leonrinkel/sam-fd/software/baremetal/inc/port.h

/* SPDX-License-Identifier: MIT */
/**
 * \file      inc/port.h
 * \brief     Definitions regarding PORT registers structure
 * \copyright Copyright (c) 2023 Leon Rinkel
 */

#ifndef SAMFD_PORT_H
#define SAMFD_PORT_H

#include <stdint.h>

/** \brief PORT registers base address */
#define PORT_ADDR 0x41000000u

/** \name PORT DIR register */
/**@{*/

/** \brief PORT DIR register structure */
typedef union
{
	/** \brief Unsigned access */
	uint32_t U;
	/** \brief Bitfield access */
	struct
	{
		/** \brief Port data direction for pin 0 */
		uint32_t DIR0:1;
		/** \brief Port data direction for pin 1 */
		uint32_t DIR1:1;
		/** \brief Port data direction for pin 2 */
		uint32_t DIR2:1;
		/** \brief Port data direction for pin 3 */
		uint32_t DIR3:1;
		/** \brief Port data direction for pin 4 */
		uint32_t DIR4:1;
		/** \brief Port data direction for pin 5 */
		uint32_t DIR5:1;
		/** \brief Port data direction for pin 6 */
		uint32_t DIR6:1;
		/** \brief Port data direction for pin 7 */
		uint32_t DIR7:1;
		/** \brief Port data direction for pin 8 */
		uint32_t DIR8:1;
		/** \brief Port data direction for pin 9 */
		uint32_t DIR9:1;
		/** \brief Port data direction for pin 10 */
		uint32_t DIR10:1;
		/** \brief Port data direction for pin 11 */
		uint32_t DIR11:1;
		/** \brief Port data direction for pin 12 */
		uint32_t DIR12:1;
		/** \brief Port data direction for pin 13 */
		uint32_t DIR13:1;
		/** \brief Port data direction for pin 14 */
		uint32_t DIR14:1;
		/** \brief Port data direction for pin 15 */
		uint32_t DIR15:1;
		/** \brief Port data direction for pin 16 */
		uint32_t DIR16:1;
		/** \brief Port data direction for pin 17 */
		uint32_t DIR17:1;
		/** \brief Port data direction for pin 18 */
		uint32_t DIR18:1;
		/** \brief Port data direction for pin 19 */
		uint32_t DIR19:1;
		/** \brief Port data direction for pin 20 */
		uint32_t DIR20:1;
		/** \brief Port data direction for pin 21 */
		uint32_t DIR21:1;
		/** \brief Port data direction for pin 22 */
		uint32_t DIR22:1;
		/** \brief Port data direction for pin 23 */
		uint32_t DIR23:1;
		/** \brief Port data direction for pin 24 */
		uint32_t DIR24:1;
		/** \brief Port data direction for pin 25 */
		uint32_t DIR25:1;
		/** \brief Port data direction for pin 26 */
		uint32_t DIR26:1;
		/** \brief Port data direction for pin 27 */
		uint32_t DIR27:1;
		/** \brief Port data direction for pin 28 */
		uint32_t DIR28:1;
		/** \brief Port data direction for pin 29 */
		uint32_t DIR29:1;
		/** \brief Port data direction for pin 30 */
		uint32_t DIR30:1;
		/** \brief Port data direction for pin 31 */
		uint32_t DIR31:1;
	} B;
} port_dir_t;

/** \brief PORT DIR register address offset */
#define PORT_DIR_OFF 0x00u

/** \brief PORT DIR register address */
#define PORT_DIR_ADDR (PORT_ADDR + PORT_DIR_OFF)

/** \brief PORT DIR register */
#define PORT_DIR (*((volatile port_dir_t*) PORT_DIR_ADDR))

/** \brief PORT DIR.DIR0 bit offset */
#define PORT_DIR_DIR0_OFF 0u
/** \brief PORT DIR.DIR0 bit mask */
#define PORT_DIR_DIR0_MSK (0x1u << PORT_DIR_DIR0_OFF)

/** \brief PORT DIR.DIR1 bit offset */
#define PORT_DIR_DIR1_OFF 1u
/** \brief PORT DIR.DIR1 bit mask */
#define PORT_DIR_DIR1_MSK (0x1u << PORT_DIR_DIR1_OFF)

/** \brief PORT DIR.DIR2 bit offset */
#define PORT_DIR_DIR2_OFF 2u
/** \brief PORT DIR.DIR2 bit mask */
#define PORT_DIR_DIR2_MSK (0x1u << PORT_DIR_DIR2_OFF)

/** \brief PORT DIR.DIR3 bit offset */
#define PORT_DIR_DIR3_OFF 3u
/** \brief PORT DIR.DIR3 bit mask */
#define PORT_DIR_DIR3_MSK (0x1u << PORT_DIR_DIR3_OFF)

/** \brief PORT DIR.DIR4 bit offset */
#define PORT_DIR_DIR4_OFF 4u
/** \brief PORT DIR.DIR4 bit mask */
#define PORT_DIR_DIR4_MSK (0x1u << PORT_DIR_DIR4_OFF)

/** \brief PORT DIR.DIR5 bit offset */
#define PORT_DIR_DIR5_OFF 5u
/** \brief PORT DIR.DIR5 bit mask */
#define PORT_DIR_DIR5_MSK (0x1u << PORT_DIR_DIR5_OFF)

/** \brief PORT DIR.DIR6 bit offset */
#define PORT_DIR_DIR6_OFF 6u
/** \brief PORT DIR.DIR6 bit mask */
#define PORT_DIR_DIR6_MSK (0x1u << PORT_DIR_DIR6_OFF)

/** \brief PORT DIR.DIR7 bit offset */
#define PORT_DIR_DIR7_OFF 7u
/** \brief PORT DIR.DIR7 bit mask */
#define PORT_DIR_DIR7_MSK (0x1u << PORT_DIR_DIR7_OFF)

/** \brief PORT DIR.DIR8 bit offset */
#define PORT_DIR_DIR8_OFF 8u
/** \brief PORT DIR.DIR8 bit mask */
#define PORT_DIR_DIR8_MSK (0x1u << PORT_DIR_DIR8_OFF)

/** \brief PORT DIR.DIR9 bit offset */
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
#define PORT_OUT_OUT18_OFF 18u
/** \brief PORT OUT.OUT18 bit mask */
#define PORT_OUT_OUT18_MSK (0x1u << PORT_OUT_OUT18_OFF)

/** \brief PORT OUT.OUT19 bit offset */
#define PORT_OUT_OUT19_OFF 19u
/** \brief PORT OUT.OUT19 bit mask */
#define PORT_OUT_OUT19_MSK (0x1u << PORT_OUT_OUT19_OFF)

/** \brief PORT OUT.OUT20 bit offset */
#define PORT_OUT_OUT20_OFF 20u
/** \brief PORT OUT.OUT20 bit mask */
#define PORT_OUT_OUT20_MSK (0x1u << PORT_OUT_OUT20_OFF)

/** \brief PORT OUT.OUT21 bit offset */
#define PORT_OUT_OUT21_OFF 21u
/** \brief PORT OUT.OUT21 bit mask */
#define PORT_OUT_OUT21_MSK (0x1u << PORT_OUT_OUT21_OFF)

/** \brief PORT OUT.OUT22 bit offset */
#define PORT_OUT_OUT22_OFF 22u
/** \brief PORT OUT.OUT22 bit mask */
#define PORT_OUT_OUT22_MSK (0x1u << PORT_OUT_OUT22_OFF)

/** \brief PORT OUT.OUT23 bit offset */
#define PORT_OUT_OUT23_OFF 23u
/** \brief PORT OUT.OUT23 bit mask */
#define PORT_OUT_OUT23_MSK (0x1u << PORT_OUT_OUT23_OFF)

/** \brief PORT OUT.OUT24 bit offset */
#define PORT_OUT_OUT24_OFF 24u
/** \brief PORT OUT.OUT24 bit mask */
#define PORT_OUT_OUT24_MSK (0x1u << PORT_OUT_OUT24_OFF)

/** \brief PORT OUT.OUT25 bit offset */
#define PORT_OUT_OUT25_OFF 25u
/** \brief PORT OUT.OUT25 bit mask */
#define PORT_OUT_OUT25_MSK (0x1u << PORT_OUT_OUT25_OFF)

/** \brief PORT OUT.OUT26 bit offset */
#define PORT_OUT_OUT26_OFF 26u
/** \brief PORT OUT.OUT26 bit mask */
#define PORT_OUT_OUT26_MSK (0x1u << PORT_OUT_OUT26_OFF)

/** \brief PORT OUT.OUT27 bit offset */
#define PORT_OUT_OUT27_OFF 27u
/** \brief PORT OUT.OUT27 bit mask */
#define PORT_OUT_OUT27_MSK (0x1u << PORT_OUT_OUT27_OFF)

/** \brief PORT OUT.OUT28 bit offset */
#define PORT_OUT_OUT28_OFF 28u
/** \brief PORT OUT.OUT28 bit mask */
#define PORT_OUT_OUT28_MSK (0x1u << PORT_OUT_OUT28_OFF)

/** \brief PORT OUT.OUT29 bit offset */
#define PORT_OUT_OUT29_OFF 29u
/** \brief PORT OUT.OUT29 bit mask */
#define PORT_OUT_OUT29_MSK (0x1u << PORT_OUT_OUT29_OFF)

/** \brief PORT OUT.OUT30 bit offset */
#define PORT_OUT_OUT30_OFF 30u
/** \brief PORT OUT.OUT30 bit mask */
#define PORT_OUT_OUT30_MSK (0x1u << PORT_OUT_OUT30_OFF)

/** \brief PORT OUT.OUT31 bit offset */
#define PORT_OUT_OUT31_OFF 31u
/** \brief PORT OUT.OUT31 bit mask */
#define PORT_OUT_OUT31_MSK (0x1u << PORT_OUT_OUT31_OFF)

/**@}*/

/** \name PORT PINCFG register */
/**@{*/

/** \brief PORT PINCFG register structure */
typedef union
{
	/** \brief Unsigned access */
	uint8_t U;
	/** \brief Bitfield access */
	struct
	{
		/** \brief Peripheral multiplexer enable */
		uint8_t PMUXEN:1;
		/** \brief Input buffer enable */
		uint8_t INEN:1;
		/** \brief Pull enable */
		uint8_t PULLEN:1;
		/** \brief Reserved */
		uint8_t :3;
		/** \brief Output driver strength selection */
		uint8_t DRVSTR:1;
		/** \brief Reserved */
		uint8_t :1;
	} B;
} port_pincfg_t;

/** \brief PORT PINCFG0 register address offset */
#define PORT_PINCFG0_OFF 0x40u
/** \brief PORT PINCFG1 register address offset */
#define PORT_PINCFG1_OFF 0x41u
/** \brief PORT PINCFG2 register address offset */
#define PORT_PINCFG2_OFF 0x42u
/** \brief PORT PINCFG3 register address offset */
#define PORT_PINCFG3_OFF 0x43u
/** \brief PORT PINCFG4 register address offset */
#define PORT_PINCFG4_OFF 0x44u
/** \brief PORT PINCFG5 register address offset */
#define PORT_PINCFG5_OFF 0x45u
/** \brief PORT PINCFG6 register address offset */
#define PORT_PINCFG6_OFF 0x46u
/** \brief PORT PINCFG7 register address offset */
#define PORT_PINCFG7_OFF 0x47u
/** \brief PORT PINCFG8 register address offset */
#define PORT_PINCFG8_OFF 0x48u
/** \brief PORT PINCFG9 register address offset */
#define PORT_PINCFG9_OFF 0x49u
/** \brief PORT PINCFG10 register address offset */
#define PORT_PINCFG10_OFF 0x4Au
/** \brief PORT PINCFG11 register address offset */
#define PORT_PINCFG11_OFF 0x4Bu
/** \brief PORT PINCFG12 register address offset */
#define PORT_PINCFG12_OFF 0x4Cu
/** \brief PORT PINCFG13 register address offset */
#define PORT_PINCFG13_OFF 0x4Du
/** \brief PORT PINCFG14 register address offset */
#define PORT_PINCFG14_OFF 0x4Eu
/** \brief PORT PINCFG15 register address offset */
#define PORT_PINCFG15_OFF 0x4Fu
/** \brief PORT PINCFG16 register address offset */
#define PORT_PINCFG16_OFF 0x50u
/** \brief PORT PINCFG17 register address offset */
#define PORT_PINCFG17_OFF 0x51u
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
/** \brief PORT PINCFG22 register */
#define PORT_PINCFG22 (*((volatile port_pincfg_t*) PORT_PINCFG22_ADDR))
/** \brief PORT PINCFG23 register */
#define PORT_PINCFG23 (*((volatile port_pincfg_t*) PORT_PINCFG23_ADDR))
/** \brief PORT PINCFG24 register */
#define PORT_PINCFG24 (*((volatile port_pincfg_t*) PORT_PINCFG24_ADDR))
/** \brief PORT PINCFG25 register */
#define PORT_PINCFG25 (*((volatile port_pincfg_t*) PORT_PINCFG25_ADDR))
/** \brief PORT PINCFG26 register */
#define PORT_PINCFG26 (*((volatile port_pincfg_t*) PORT_PINCFG26_ADDR))
/** \brief PORT PINCFG27 register */
#define PORT_PINCFG27 (*((volatile port_pincfg_t*) PORT_PINCFG27_ADDR))
/** \brief PORT PINCFG28 register */
#define PORT_PINCFG28 (*((volatile port_pincfg_t*) PORT_PINCFG28_ADDR))
/** \brief PORT PINCFG29 register */
#define PORT_PINCFG29 (*((volatile port_pincfg_t*) PORT_PINCFG29_ADDR))
/** \brief PORT PINCFG30 register */
#define PORT_PINCFG30 (*((volatile port_pincfg_t*) PORT_PINCFG30_ADDR))
/** \brief PORT PINCFG31 register */
#define PORT_PINCFG31 (*((volatile port_pincfg_t*) PORT_PINCFG31_ADDR))

/** \brief PORT PINCFG.PMUXEN bit offset */
#define PORT_PINCFG_PMUXEN_OFF 0u
/** \brief PORT PINCFG.PMUXEN bit mask */
#define PORT_PINCFG_PMUXEN_MSK (0x1u << PORT_PINCFG_PMUXEN_OFF)

/** \brief PORT PINCFG.INEN bit offset */
#define PORT_PINCFG_INEN_OFF 1u
/** \brief PORT PINCFG.INEN bit mask */
#define PORT_PINCFG_INEN_MSK (0x1u << PORT_PINCFG_INEN_OFF)

/** \brief PORT PINCFG.PULLEN bit offset */
#define PORT_PINCFG_PULLEN_OFF 2u
/** \brief PORT PINCFG.PULLEN bit mask */
#define PORT_PINCFG_PULLEN_MSK (0x1u << PORT_PINCFG_PULLEN_OFF)

/** \brief PORT PINCFG.DRVSTR bit offset */
#define PORT_PINCFG_DRVSTR_OFF 6u
/** \brief PORT PINCFG.DRVSTR bit mask */
#define PORT_PINCFG_DRVSTR_MSK (0x1u << PORT_PINCFG_DRVSTR_OFF)

/**@}*/

/** \name PORT PMUX register */
/**@{*/

/** \brief PORT PMUX register structure */
typedef union
{
	/** \brief Unsigned access */
	uint8_t U;
	/** \brief Bitfield access */
	struct
	{
		/** \brief Peripheral multiplexing for even-numbered pin */
		uint8_t PMUXE:4;
		/** \brief Peripheral multiplexing for odd-numbered pin */
		uint8_t PMUXO:4;
	} B;
} port_pmux_t;

/** \brief PORT PMUX0 register address offset */
#define PORT_PMUX0_OFF 0x30u
/** \brief PORT PMUX1 register address offset */
#define PORT_PMUX1_OFF 0x31u
/** \brief PORT PMUX2 register address offset */
#define PORT_PMUX2_OFF 0x32u
/** \brief PORT PMUX3 register address offset */
#define PORT_PMUX3_OFF 0x33u
/** \brief PORT PMUX4 register address offset */
#define PORT_PMUX4_OFF 0x34u
/** \brief PORT PMUX5 register address offset */
#define PORT_PMUX5_OFF 0x35u
/** \brief PORT PMUX6 register address offset */
#define PORT_PMUX6_OFF 0x36u
/** \brief PORT PMUX7 register address offset */
#define PORT_PMUX7_OFF 0x37u
/** \brief PORT PMUX8 register address offset */
#define PORT_PMUX8_OFF 0x38u
/** \brief PORT PMUX9 register address offset */
#define PORT_PMUX9_OFF 0x39u
/** \brief PORT PMUX10 register address offset */
#define PORT_PMUX10_OFF 0x3Au
/** \brief PORT PMUX11 register address offset */
#define PORT_PMUX11_OFF 0x3Bu
/** \brief PORT PMUX12 register address offset */
#define PORT_PMUX12_OFF 0x3Cu
/** \brief PORT PMUX13 register address offset */
#define PORT_PMUX13_OFF 0x3Du
/** \brief PORT PMUX14 register address offset */
#define PORT_PMUX14_OFF 0x3Eu
/** \brief PORT PMUX15 register address offset */
#define PORT_PMUX15_OFF 0x3Fu

/** \brief PORT PMUX0 register address */
#define PORT_PMUX0_ADDR (PORT_ADDR + PORT_PMUX0_OFF)
/** \brief PORT PMUX1 register address */
#define PORT_PMUX1_ADDR (PORT_ADDR + PORT_PMUX1_OFF)
/** \brief PORT PMUX2 register address */
#define PORT_PMUX2_ADDR (PORT_ADDR + PORT_PMUX2_OFF)
/** \brief PORT PMUX3 register address */
#define PORT_PMUX3_ADDR (PORT_ADDR + PORT_PMUX3_OFF)
/** \brief PORT PMUX4 register address */
#define PORT_PMUX4_ADDR (PORT_ADDR + PORT_PMUX4_OFF)
/** \brief PORT PMUX5 register address */
#define PORT_PMUX5_ADDR (PORT_ADDR + PORT_PMUX5_OFF)
/** \brief PORT PMUX6 register address */
#define PORT_PMUX6_ADDR (PORT_ADDR + PORT_PMUX6_OFF)
/** \brief PORT PMUX7 register address */
#define PORT_PMUX7_ADDR (PORT_ADDR + PORT_PMUX7_OFF)
/** \brief PORT PMUX8 register address */
#define PORT_PMUX8_ADDR (PORT_ADDR + PORT_PMUX8_OFF)
/** \brief PORT PMUX9 register address */
#define PORT_PMUX9_ADDR (PORT_ADDR + PORT_PMUX9_OFF)
/** \brief PORT PMUX10 register address */
#define PORT_PMUX10_ADDR (PORT_ADDR + PORT_PMUX10_OFF)
/** \brief PORT PMUX11 register address */
#define PORT_PMUX11_ADDR (PORT_ADDR + PORT_PMUX11_OFF)
/** \brief PORT PMUX12 register address */
#define PORT_PMUX12_ADDR (PORT_ADDR + PORT_PMUX12_OFF)
/** \brief PORT PMUX13 register address */
#define PORT_PMUX13_ADDR (PORT_ADDR + PORT_PMUX13_OFF)
/** \brief PORT PMUX14 register address */
#define PORT_PMUX14_ADDR (PORT_ADDR + PORT_PMUX14_OFF)
/** \brief PORT PMUX15 register address */
#define PORT_PMUX15_ADDR (PORT_ADDR + PORT_PMUX15_OFF)

/** \brief PORT PMUX0 register */
#define PORT_PMUX0 (*((volatile port_pmux_t*) PORT_PMUX0_ADDR))
/** \brief PORT PMUX1 register */
#define PORT_PMUX1 (*((volatile port_pmux_t*) PORT_PMUX1_ADDR))
/** \brief PORT PMUX2 register */
#define PORT_PMUX2 (*((volatile port_pmux_t*) PORT_PMUX2_ADDR))
/** \brief PORT PMUX3 register */
#define PORT_PMUX3 (*((volatile port_pmux_t*) PORT_PMUX3_ADDR))
/** \brief PORT PMUX4 register */
#define PORT_PMUX4 (*((volatile port_pmux_t*) PORT_PMUX4_ADDR))
/** \brief PORT PMUX5 register */
#define PORT_PMUX5 (*((volatile port_pmux_t*) PORT_PMUX5_ADDR))
/** \brief PORT PMUX6 register */
#define PORT_PMUX6 (*((volatile port_pmux_t*) PORT_PMUX6_ADDR))
/** \brief PORT PMUX7 register */
#define PORT_PMUX7 (*((volatile port_pmux_t*) PORT_PMUX7_ADDR))
/** \brief PORT PMUX8 register */
#define PORT_PMUX8 (*((volatile port_pmux_t*) PORT_PMUX8_ADDR))
/** \brief PORT PMUX9 register */
#define PORT_PMUX9 (*((volatile port_pmux_t*) PORT_PMUX9_ADDR))
/** \brief PORT PMUX10 register */
#define PORT_PMUX10 (*((volatile port_pmux_t*) PORT_PMUX10_ADDR))
/** \brief PORT PMUX11 register */
#define PORT_PMUX11 (*((volatile port_pmux_t*) PORT_PMUX11_ADDR))
/** \brief PORT PMUX12 register */
#define PORT_PMUX12 (*((volatile port_pmux_t*) PORT_PMUX12_ADDR))
/** \brief PORT PMUX13 register */
#define PORT_PMUX13 (*((volatile port_pmux_t*) PORT_PMUX13_ADDR))
/** \brief PORT PMUX14 register */
#define PORT_PMUX14 (*((volatile port_pmux_t*) PORT_PMUX14_ADDR))
/** \brief PORT PMUX15 register */
#define PORT_PMUX15 (*((volatile port_pmux_t*) PORT_PMUX15_ADDR))

/** \brief PORT PMUX.PMUXE bit offset */
#define PORT_PMUX_PMUXE_OFF 0u
/** \brief PORT PMUX.PMUXE bit mask */
#define PORT_PMUX_PMUXE_MSK (0xFu << PORT_PMUX_PMUXE)

/** \brief PORT PMUX.PMUXO bit offset */
#define PORT_PMUX_PMUXO_OFF 4u
/** \brief PORT PMUX.PMUXO bit mask */
#define PORT_PMUX_PMUXO_MSK (0xFu << PORT_PMUX_PMUXO)

/**@}*/

#endif /* SAMFD_PORT_H */
